wyattwww/swelldone-rudda/concept2-steerer-fs/images/steerer-fs-4.png

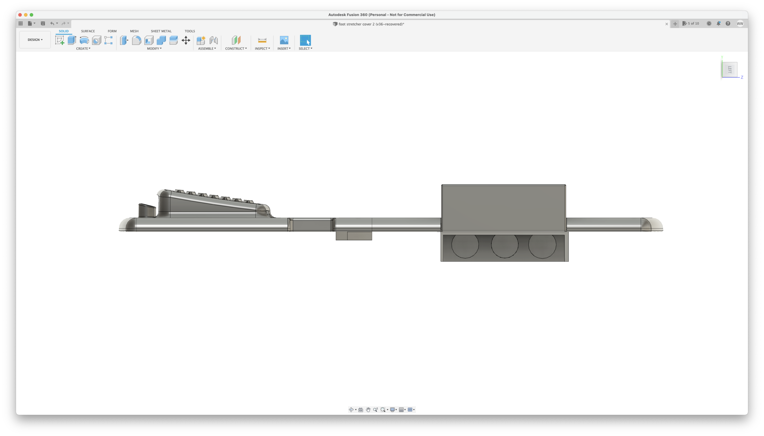
concept2-steerer-fs/images/steerer-fs-4.png
