wyattwww/swelldone-rudda/concept2-steerer-fs/images/steerer-fs-5.png

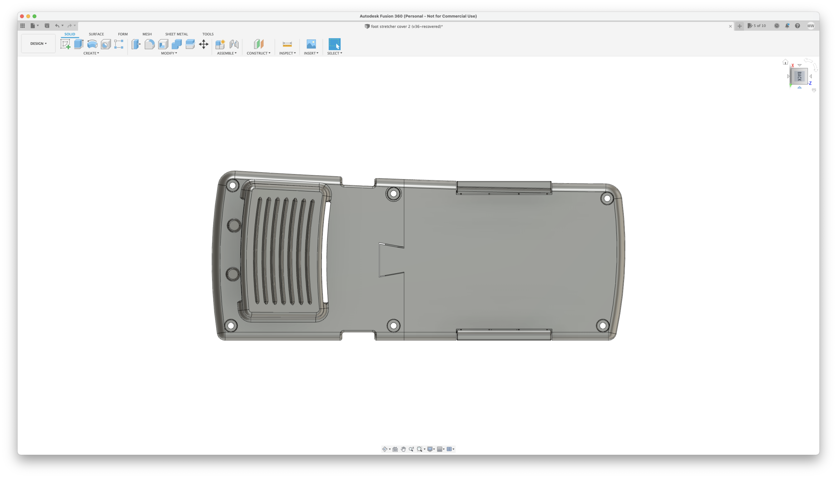
concept2-steerer-fs/images/steerer-fs-5.png
