wyattwww/swelldone-rudda/concept2-steerer/images/steerer-6.png

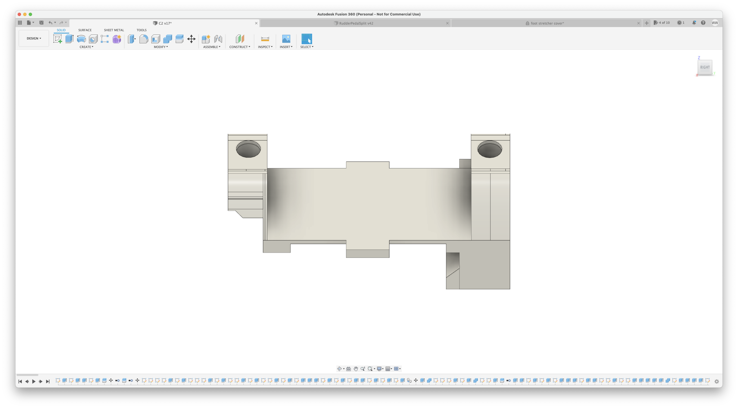
concept2-steerer/images/steerer-6.png
