wyattwww/swelldone-rudda/concept2-steerer/images/steerer-8.png

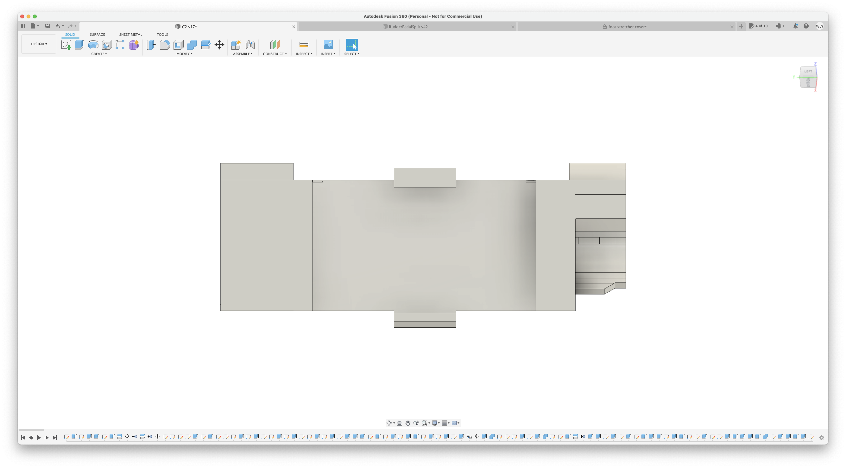
concept2-steerer/images/steerer-8.png
