wyattwww/swelldone-rudda/kayakpro-pedals/images/pedals-2.png

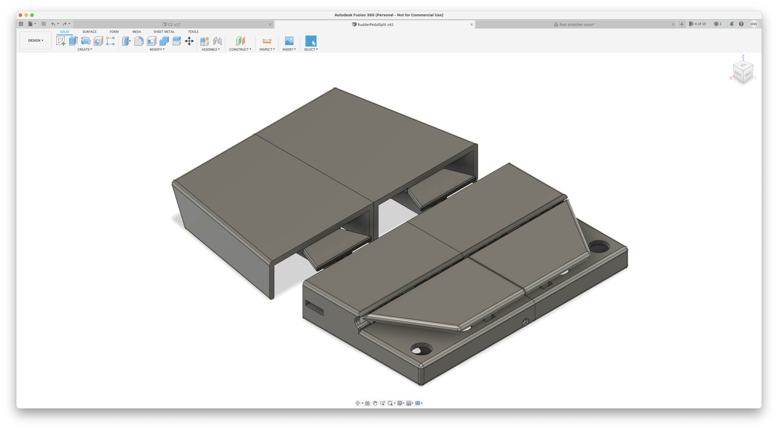
kayakpro-pedals/images/pedals-2.png
