wyattwww/swelldone-rudda/kayakpro-pedals/images/pedals-3.png

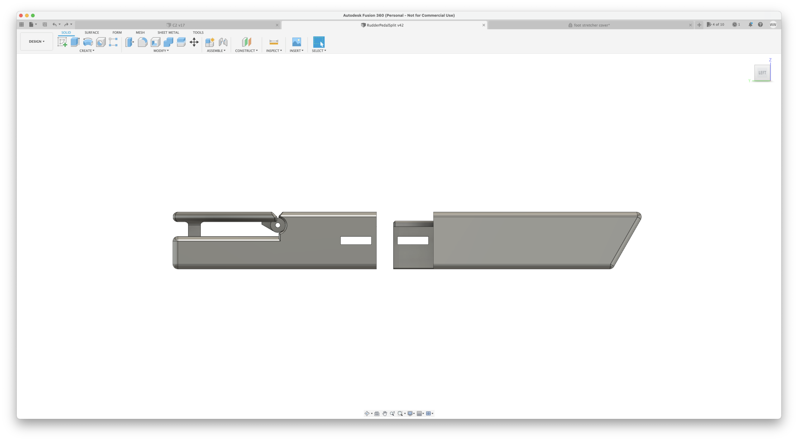
kayakpro-pedals/images/pedals-3.png
