wyattwww/swelldone-rudda/kayakpro-pedals/images/pedals-4.png

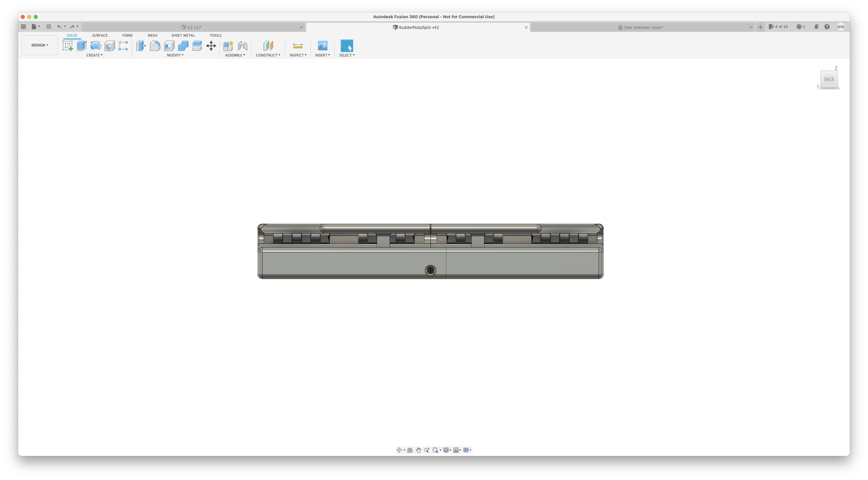
kayakpro-pedals/images/pedals-4.png
