wyattwww/swelldone-rudda/kayakpro-pedals/images/pedals-5.png

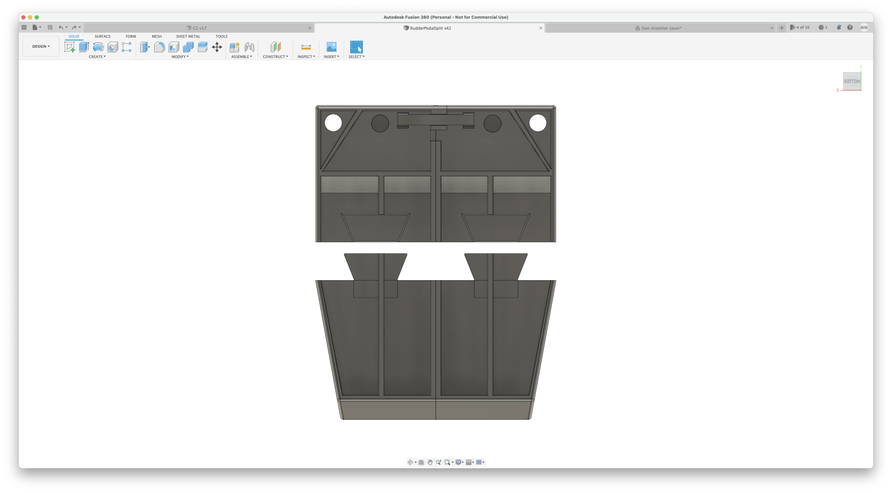
kayakpro-pedals/images/pedals-5.png
