wyattwww/swelldone-rudda/kayakpro-pedals/images/pedals-6.png

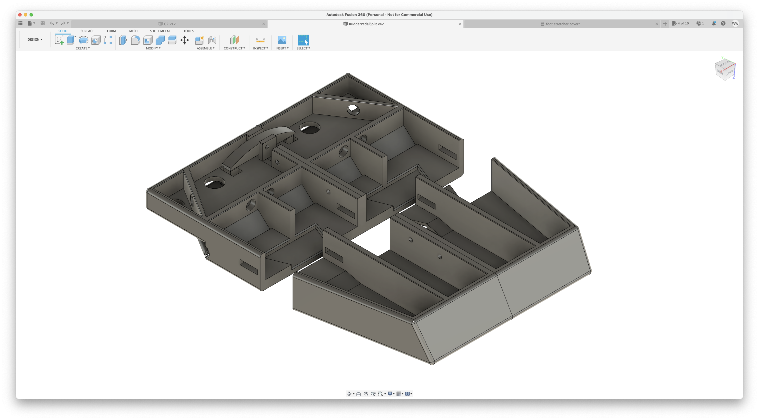
kayakpro-pedals/images/pedals-6.png
